obskyr/f-ramune/software/channelio.hpp

#ifndef CHANNELIO_HPP
#define CHANNELIO_HPP

#include <stdint.h>
#include <SPI.h>
#include "fastpins.hpp"

// Base classes

template <class T>
class InputChannel
{
public:
    virtual ~InputChannel() {}
    virtual T input() = 0;
    virtual void initInput() = 0;
};

template <class T>
class OutputChannel
{
public:
    virtual ~OutputChannel() {}
    virtual void output(T n) = 0;
    virtual void initOutput() = 0;
};

template <class T>
class InputOutputChannel : virtual public InputChannel<T>,
                           virtual public OutputChannel<T>
{
public:
    virtual ~InputOutputChannel() {}
};

// Channel sets (multiple channels triggered via a single object)

template <class OutputType, class Contained>
class InputChannelSet : virtual public InputChannel<OutputType>
{
public:
    InputChannelSet(unsigned int numChannels,
                    Contained* channels[]);
    OutputType input();
    void initInput();
private:
    unsigned int _numChannels;
    Contained** _inputChannels;
};

template <class OutputType, class Contained>
class OutputChannelSet : virtual public OutputChannel<OutputType>
{
public:
    OutputChannelSet(unsigned int numChannels,
                     Contained* channels[]);
    void output(OutputType n);
    void initOutput();
private:
    unsigned int _numChannels;
    Contained** _outputChannels;
};

template <class OutputType, class Contained>
class InputOutputChannelSet :
    virtual public InputChannelSet<OutputType, Contained>,
    virtual public OutputChannelSet<OutputType, Contained>,
    virtual public InputOutputChannel<OutputType>
{
public:
    InputOutputChannelSet(unsigned int numChannels,
                          Contained* channels[]);
private:
    unsigned int _numChannels;
    Contained** _channels;
};

// Specific IO types

template <class T>
class Output_ShiftRegister : public OutputChannel<T>
{
public:
    Output_ShiftRegister(unsigned int dataPin, unsigned int shiftPin,
                         unsigned int latchPin, unsigned int numBits);
    void output(T n);
    void initOutput();
private:
    PinPortInfo _dataPin;
    PinPortInfo _shiftPin;
    PinPortInfo _latchPin;
    unsigned int _numBits;
};

template <class T>
class Output_Spi : public OutputChannel<T>
{
public:
    Output_Spi(uint32_t frequency, uint8_t mode);
    virtual void output(T n);
    virtual void initOutput();
private:
    SPISettings _settings;
};

template <class T>
class Output_SpiShiftRegister : public Output_Spi<T>
{
public:
    Output_SpiShiftRegister(uint32_t frequency, uint8_t spiMode, uint8_t latchPin);
    void output(T n);
    void initOutput();
private:
    PinPortInfo _latchPin;
};

class InputOutput_Port : public InputOutputChannel<uint8_t>
{
public:
    InputOutput_Port(uint8_t inputMode,
                     volatile uint8_t* inputRegister,
                     volatile uint8_t* outputRegister,
                     volatile uint8_t* directionRegister,
                     unsigned int portStartBit,
                     unsigned int valueStartBit,
                     unsigned int numBits);
    uint8_t input();
    void output(uint8_t n);
    void initInput();
    void initOutput();
private:
    uint8_t _inputMode;
    volatile uint8_t* _inputRegister;
    volatile uint8_t* _outputRegister;
    volatile uint8_t* _directionRegister;
    unsigned int _portStartBit;
    unsigned int _valueStartBit;
    unsigned int _numBits;
    uint8_t _portMask;
};

// This very, very strange way of separating declaration from implementation
// was wrought upon this world not by my hand, but by a combination of C++'s
// questionable handling of templates and Arduino's questionable rigidity
// in code structure and file extensions. Bon appetit.
#define INCLUDING_CHANNELIO_TEMPLATES
#include "channelio.cpp"
#undef INCLUDING_CHANNELIO_TEMPLATES

#endif
